oveljosland/ekg-project/step-down/step-down/step-down.kicad_sch

## KiCad design step-down/step-down/step-down.kicad_sch (2025-02-12)

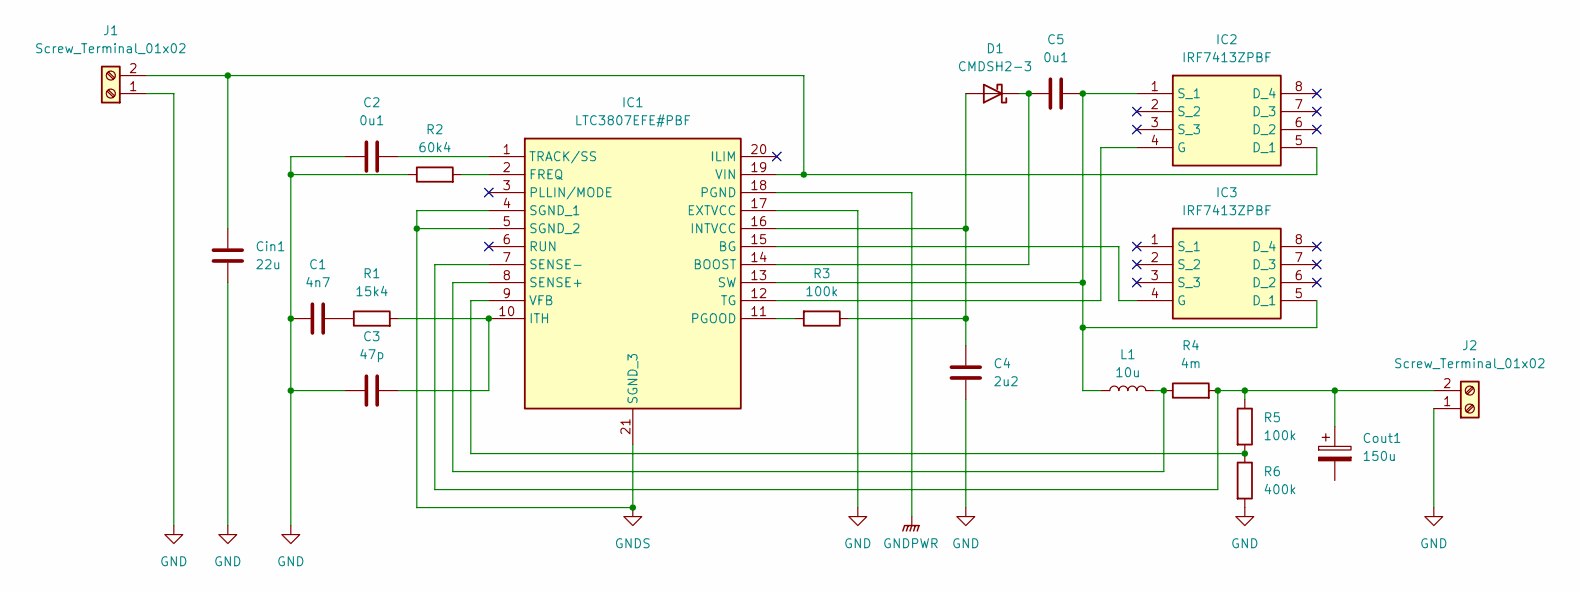
[picture p5: schematic step-down.kicad_sch]

Parts:
C1: 4n7; CAP_CS0603_YAG
C2, C5: 0u1; CAP_CS0402_YAG
C3: 47p; CAP_CS1206_YAG
C4: 2u2; CC0402KRX5R7BB225
Cin1: 22u; CAP_CC1206_YAG
Cout1: 150u; TAZH157J010LBSZ0H00
D1: CMDSH2-3; CMDSH2-3_TR_PBFREE
IC1: LTC3807EFE#PBF; Mouser Part Number 584-LTC3807EFE#PBF
IC2, IC3: IRF7413ZPBF; Mouser Part Number 942-IRF7413ZPBF
J1, J2: Screw_Terminal_01x02; 1725656
L1: 10u; AISC-1008F-100G-T
R1: 15k4; ERJ-XGNF1542Y
R2: 60k4; ERJ-XGNF6042Y
R3, R5: 100k; ERJ-XGNF1003Y
R4: 4m; KRL6432D-C-R004-F-T5
R6: 400k; ERJ-XGNF4023Y

Connections:
GND: C1.1, C2.1, C3.2, C4.2, Cin1.2, IC1.17 (EXTVCC), J1.1, J2.1, R2.1, R6.2
GNDPWR: IC1.18 (PGND)
GNDS: IC1.4 (SGND_1), IC1.5 (SGND_2), IC1.21 (SGND_3)
unnamed: C1.2, R1.1
unnamed: C2.2, IC1.1 (TRACK/SS)
unnamed: C3.1, IC1.10 (ITH), R1.2
unnamed: C4.1, D1.2 (A), IC1.16 (INTVCC), R3.1
unnamed: C5.1, D1.1 (K), IC1.14 (BOOST)
unnamed: C5.2, IC1.13 (SW), IC2.1 (S_1), IC3.5 (D_1), L1.1
unnamed: Cin1.1, IC1.19 (VIN), IC2.5 (D_1), J1.2
unnamed: Cout1.1, IC1.7 (SENSE-), J2.2, R4.2, R5.1
unnamed: IC1.2 (FREQ), R2.2
unnamed: IC1.8 (SENSE+), L1.2, R4.1
unnamed: IC1.9 (VFB), R5.2, R6.1
unnamed: IC1.11 (PGOOD), R3.2
unnamed: IC1.12 (TG), IC2.4 (G)
unnamed: IC1.15 (BG), IC3.4 (G)
